istarendil/vibration_logger/cad/case/Case1.JPG

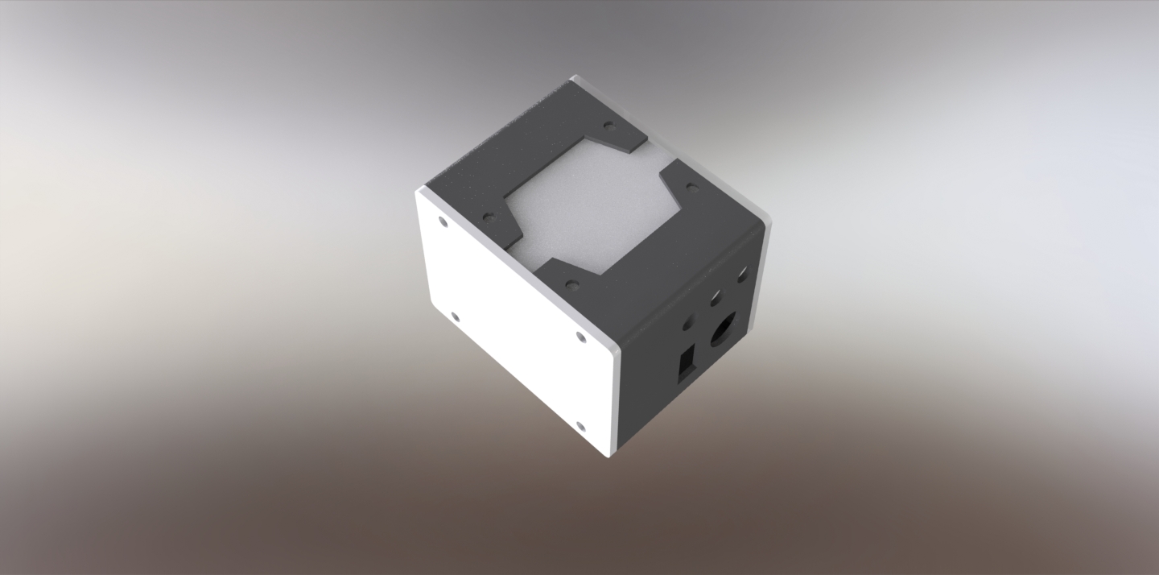
cad/case/Case1.JPG
