istarendil/vibration_logger/cad/case/Case2.JPG

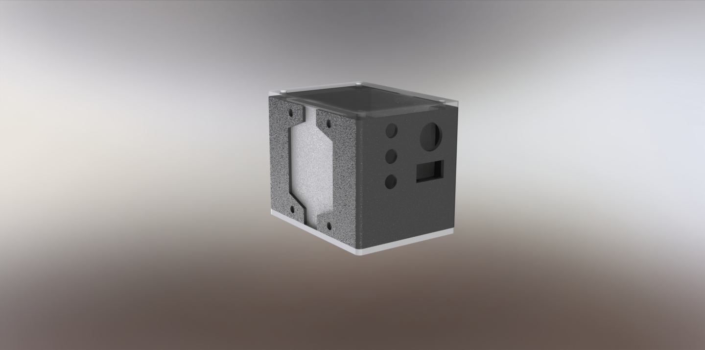
cad/case/Case2.JPG
