istarendil/vibration_logger/doc/img/3D-1.jpg

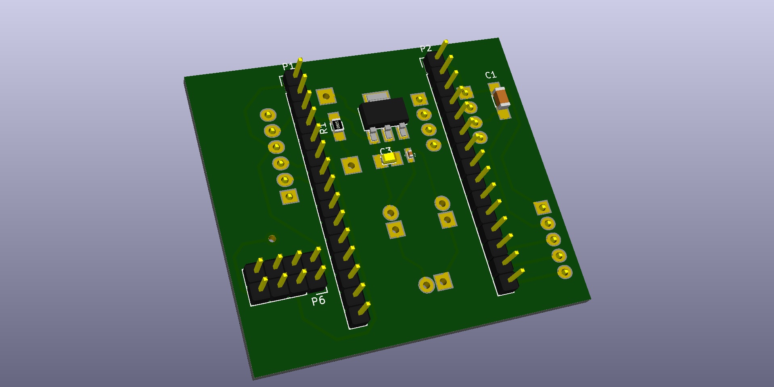
doc/img/3D-1.jpg
