istarendil/vibration_logger/doc/img/3D-2.jpg

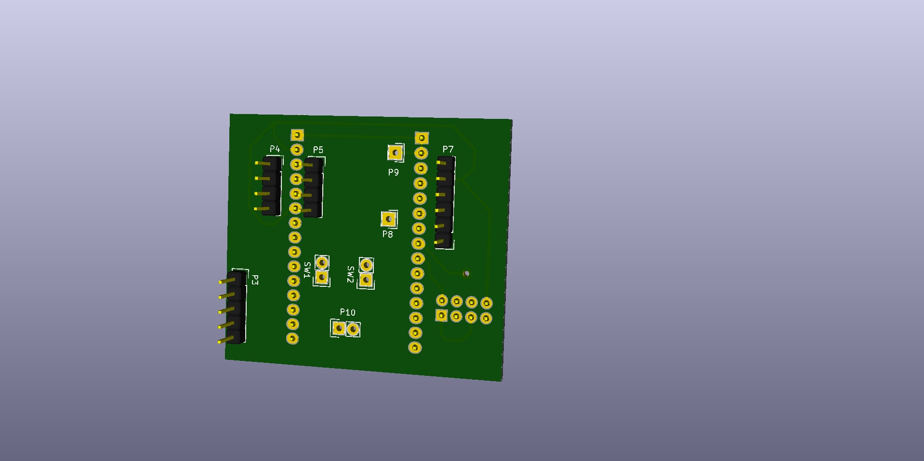
doc/img/3D-2.jpg
