istarendil/vibration_logger/doc/img/2016-09-04 22.12.24.jpg

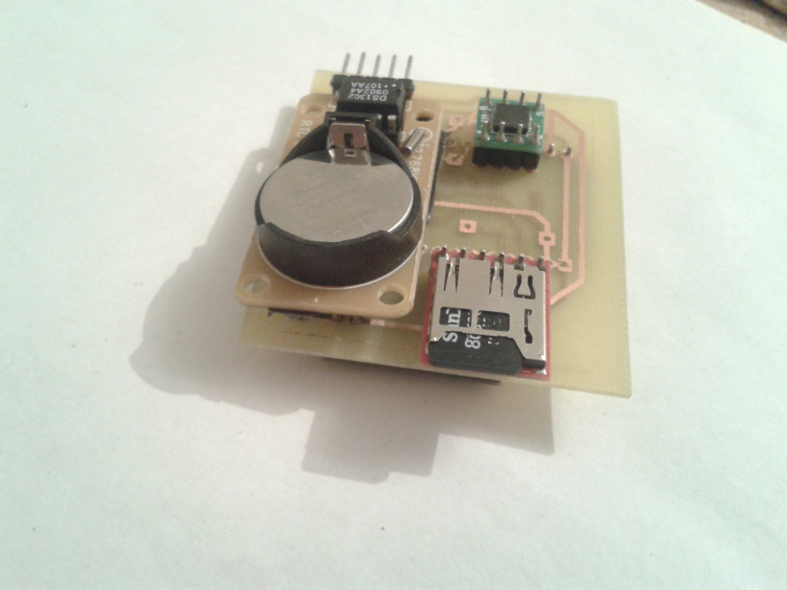
doc/img/2016-09-04 22.12.24.jpg
