istarendil/vibration_logger/doc/img/2016-09-04 22.13.55.jpg

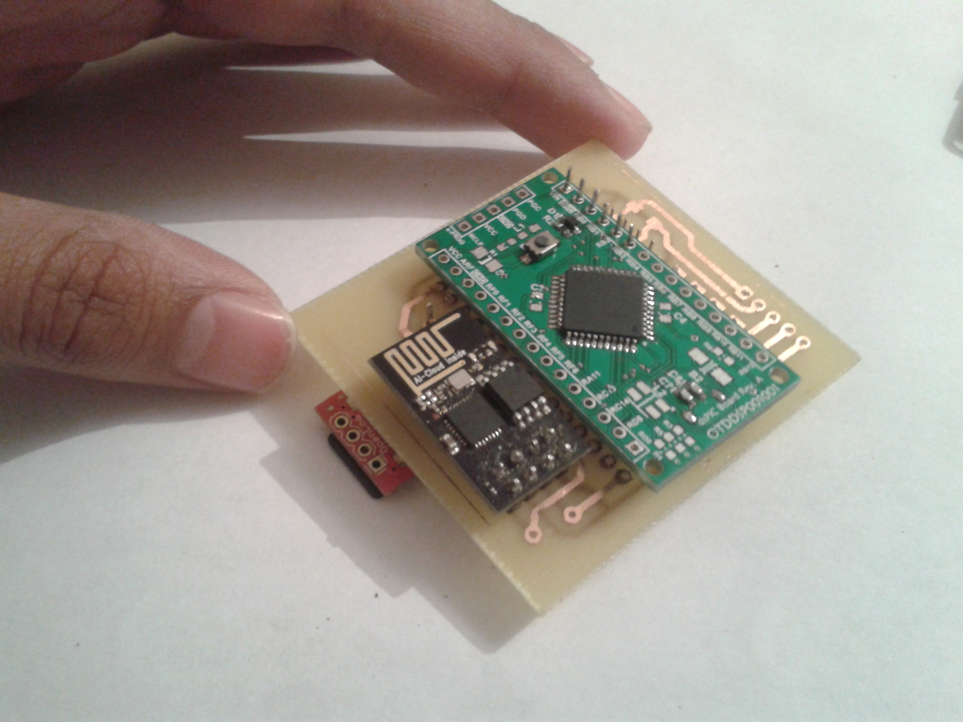
doc/img/2016-09-04 22.13.55.jpg
