istarendil/vibration_logger/doc/img/2016-10-13 19.51.26.jpg

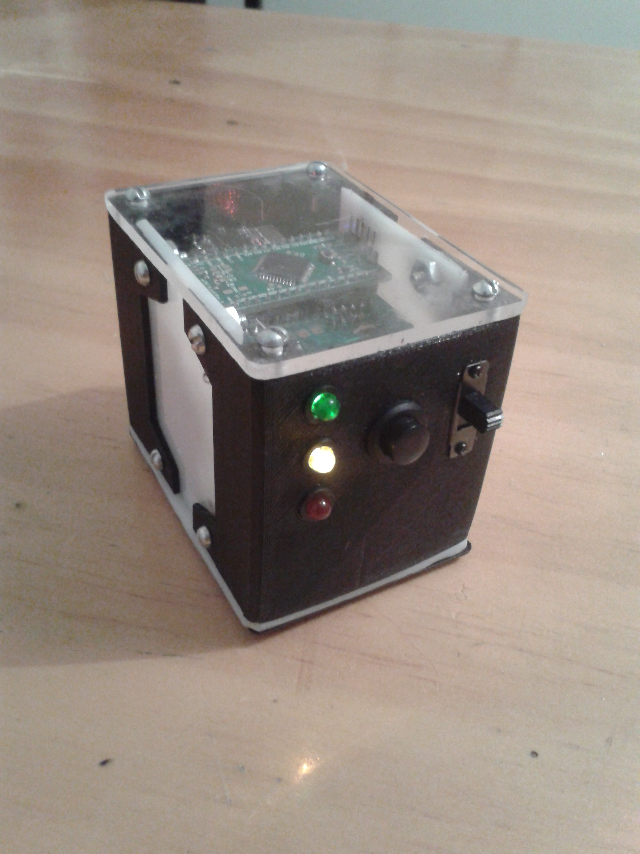
doc/img/2016-10-13 19.51.26.jpg
