istarendil/vibration_logger/doc/img/2016-10-13 19.52.44.jpg

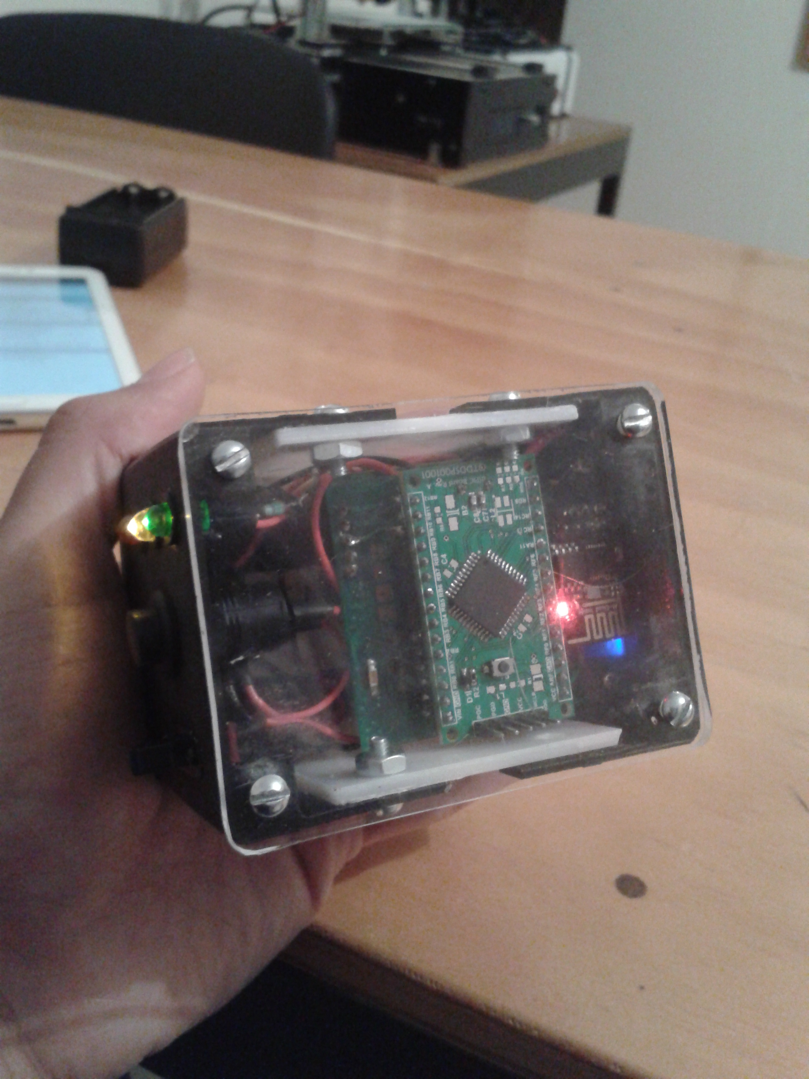
doc/img/2016-10-13 19.52.44.jpg
