istarendil/vibration_logger/doc/img/2016-10-13 19.56.58.jpg

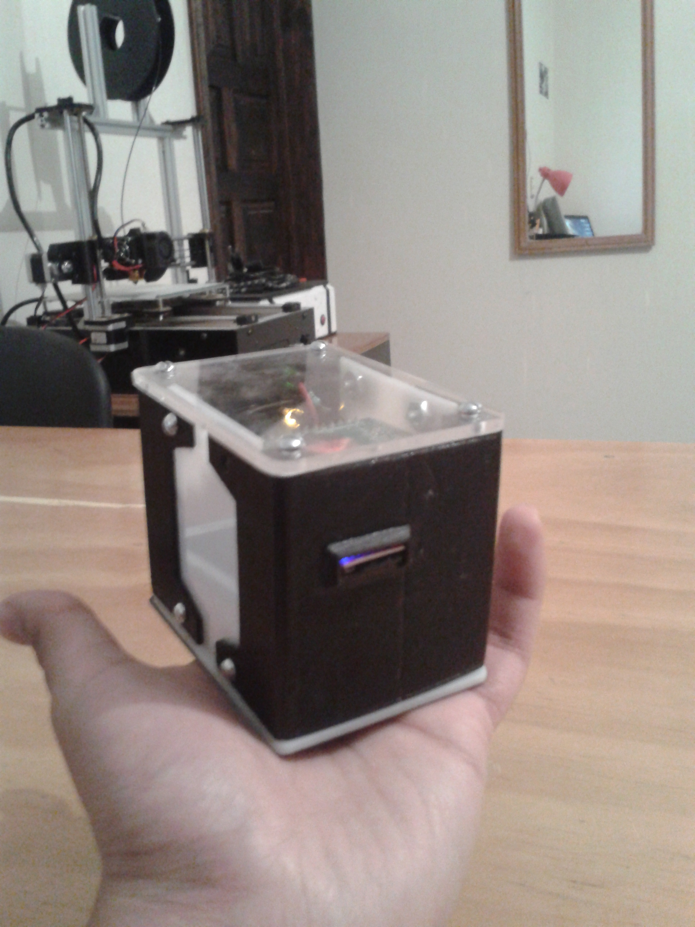
doc/img/2016-10-13 19.56.58.jpg
