istarendil/vibration_logger/doc/img/Foto1.jpg

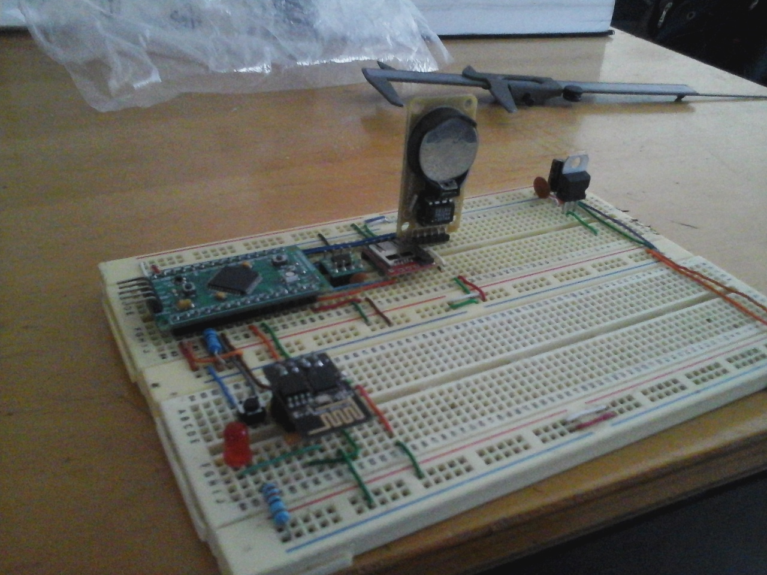
doc/img/Foto1.jpg
