istarendil/vibration_logger/doc/img/Foto2.jpg

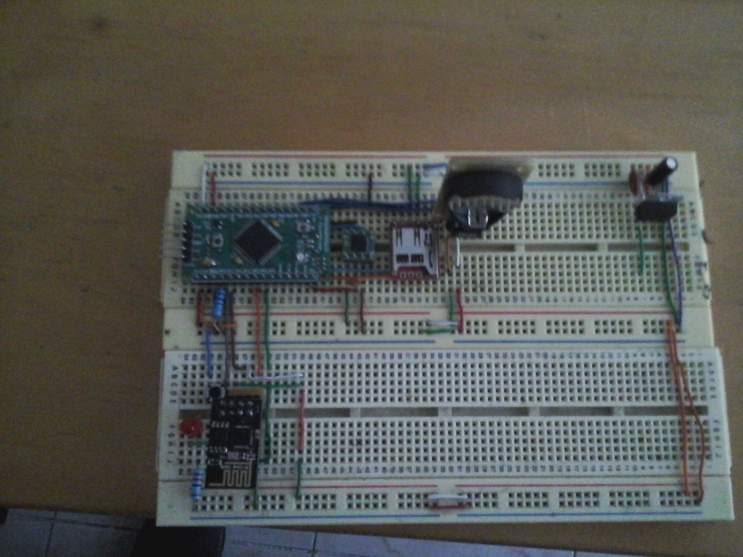
doc/img/Foto2.jpg
