istarendil/vibration_logger/doc/img/Interfaz Web.jpg

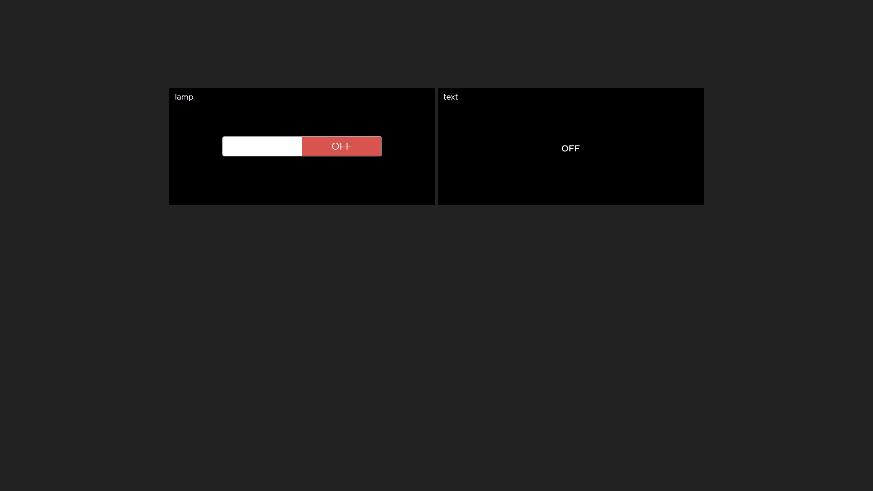
doc/img/Interfaz Web.jpg
