istarendil/vibration_logger/doc/img/PCB.jpg

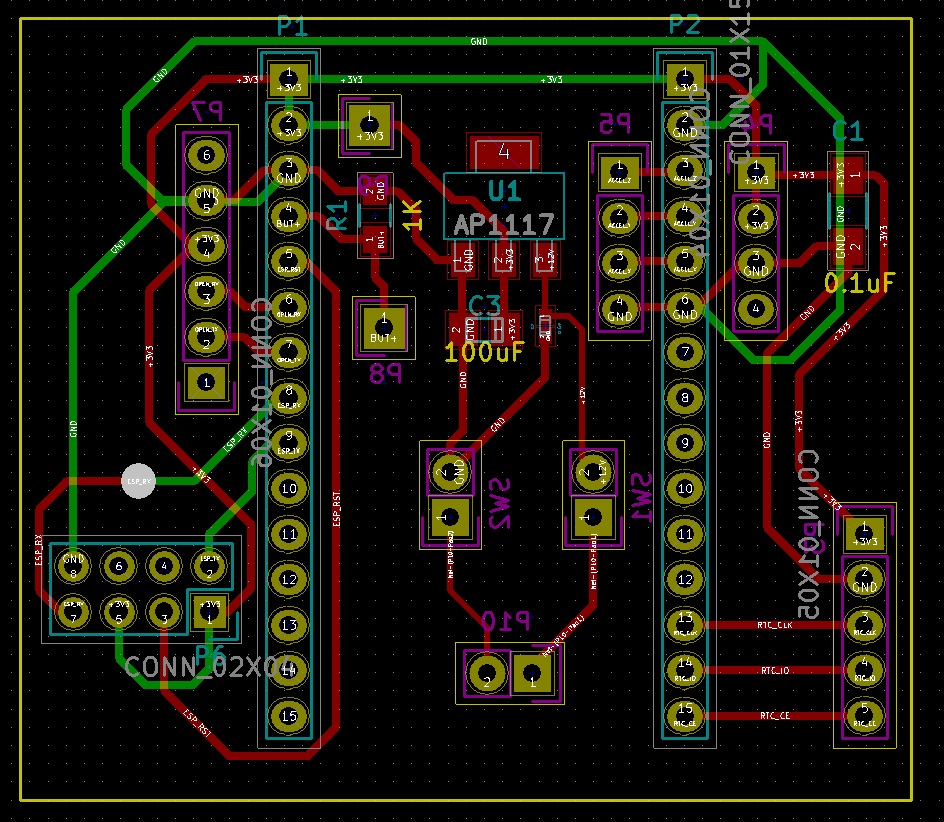
doc/img/PCB.jpg
